IOIO72/scad-amiga-clock/20210601_144001.jpg

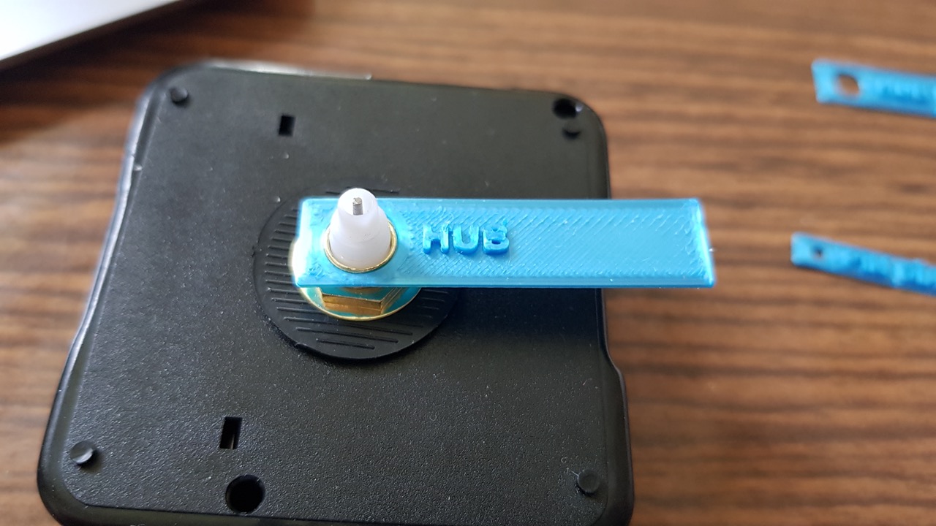
20210601_144001.jpg
