IOIO72/scad-amiga-clock/20210601_144141.jpg

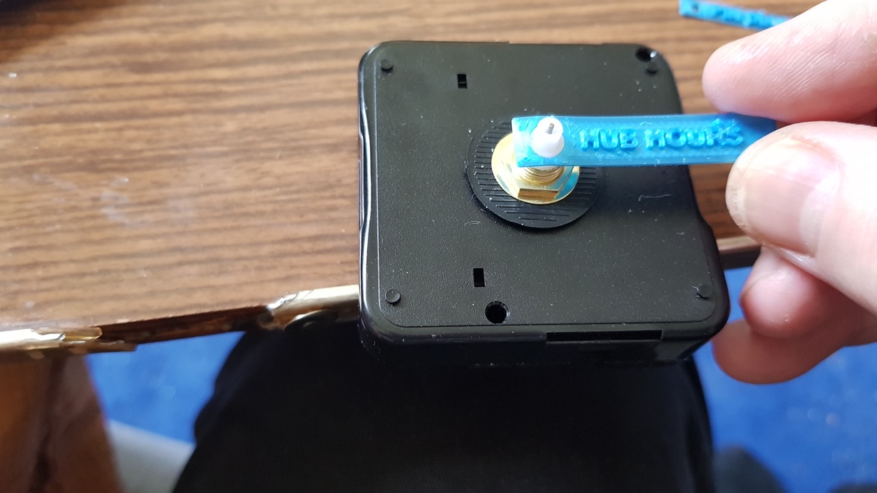
20210601_144141.jpg
