IOIO72/scad-amiga-clock/20210601_144154.jpg

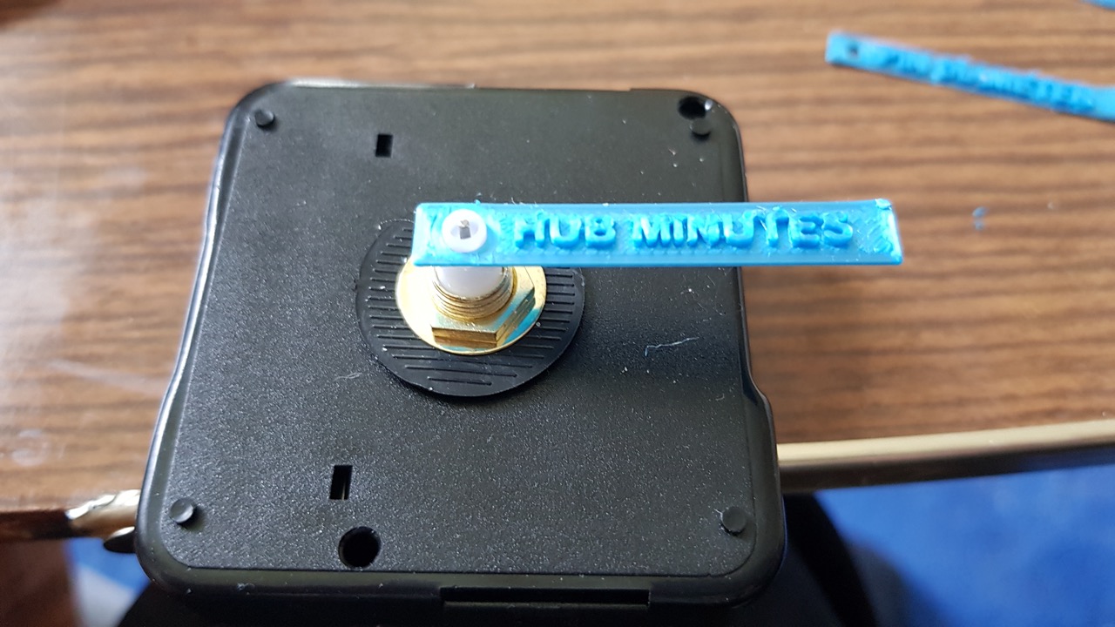
20210601_144154.jpg
