IOIO72/scad-amiga-clock/20210601_144229.jpg

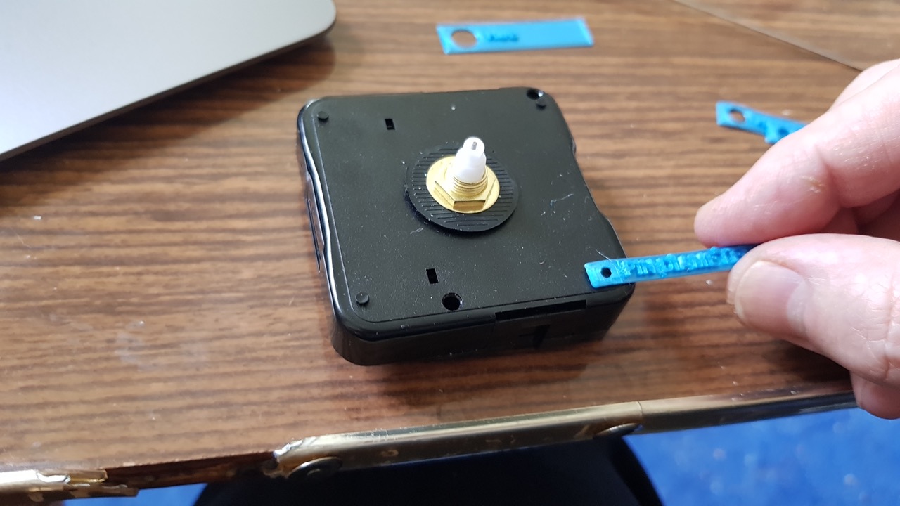
20210601_144229.jpg
