IOIO72/scad-amiga-clock/20210601_170503.jpg

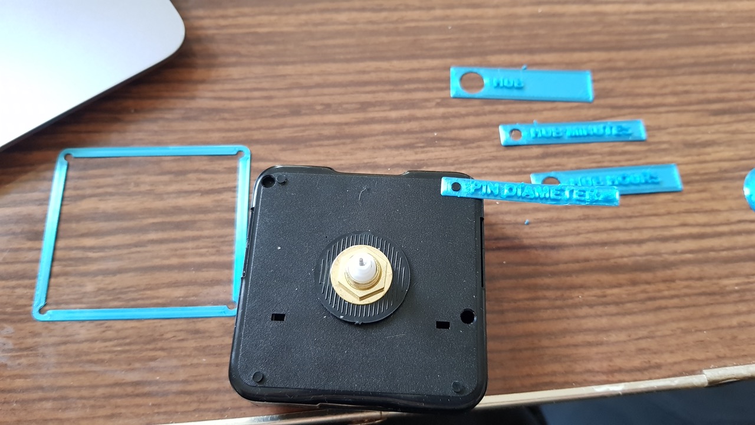
20210601_170503.jpg
