IOIO72/scad-amiga-clock/20210601_170538.jpg

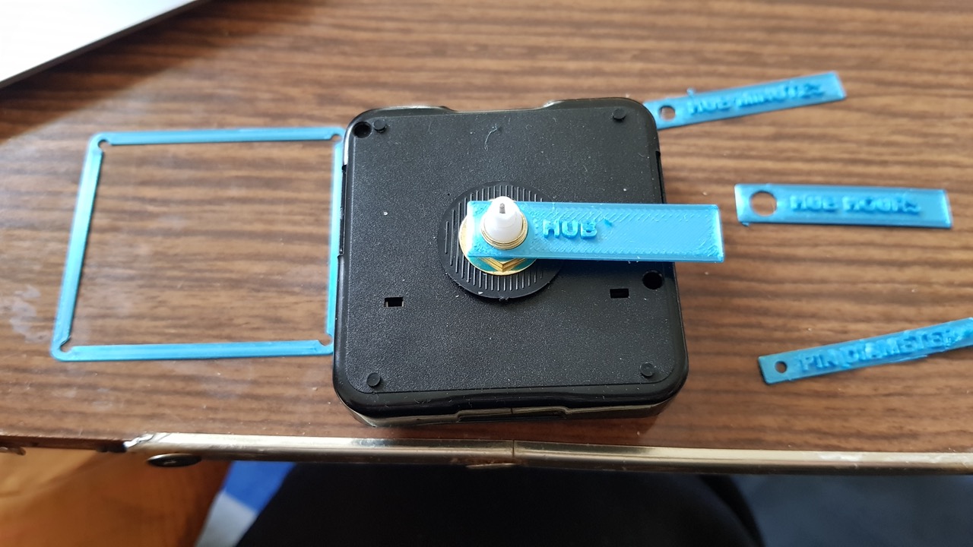
20210601_170538.jpg
