IOIO72/scad-amiga-clock/20210601_170613.jpg

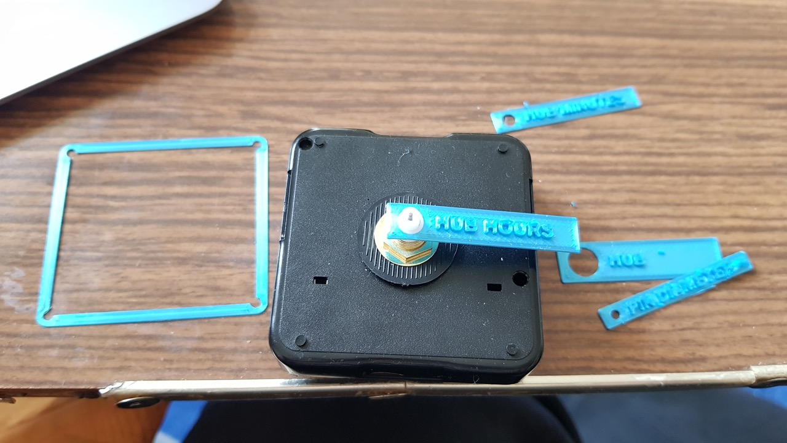
20210601_170613.jpg
