IOIO72/scad-amiga-clock/20210601_170634.jpg

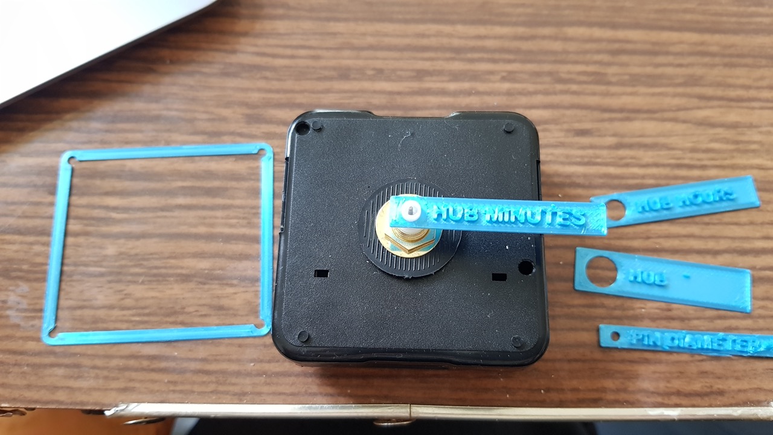
20210601_170634.jpg
