IOIO72/scad-amiga-clock/20210601_195533.jpg

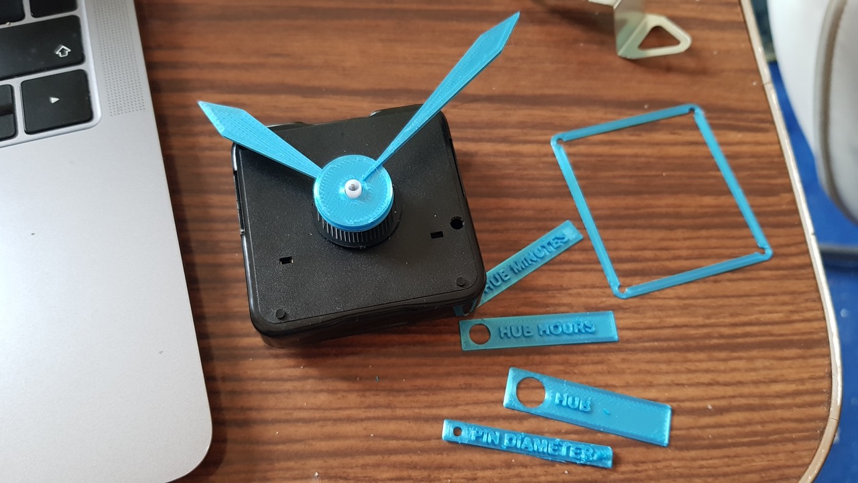
20210601_195533.jpg
