IOIO72/scad-amiga-clock/20210601_195553.jpg

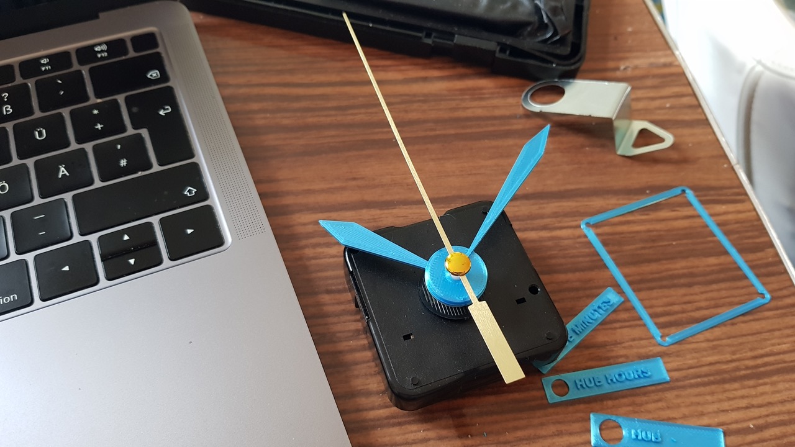
20210601_195553.jpg
