IOIO72/scad-amiga-clock/20210601_195704.jpg

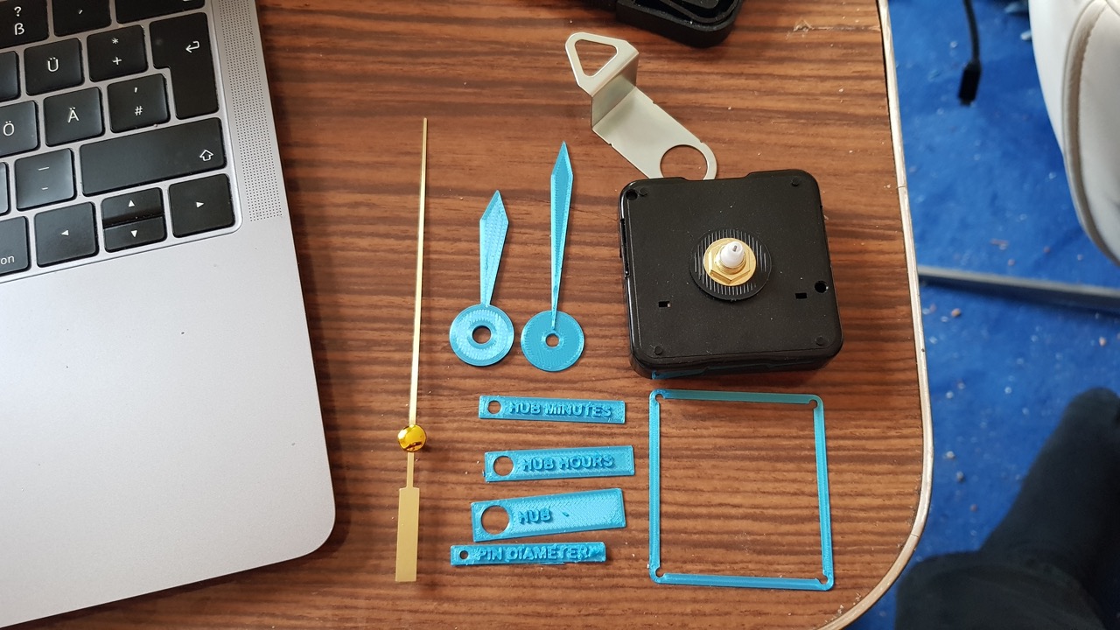
20210601_195704.jpg
