IOIO72/scad-amiga-clock/20210601_195735.jpg

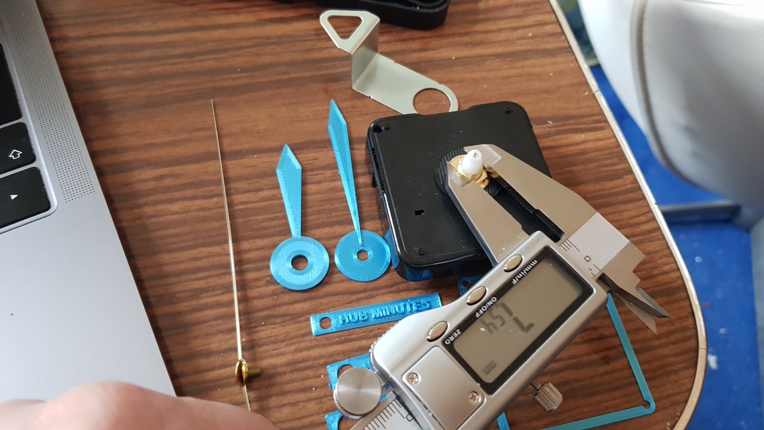
20210601_195735.jpg
