IOIO72/scad-amiga-clock/20210601_195748.jpg

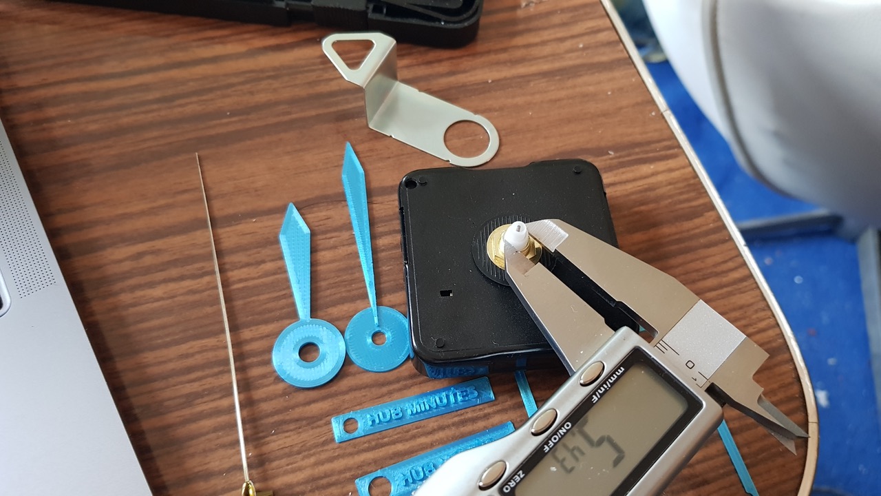
20210601_195748.jpg
