IOIO72/scad-amiga-clock/20210601_195756.jpg

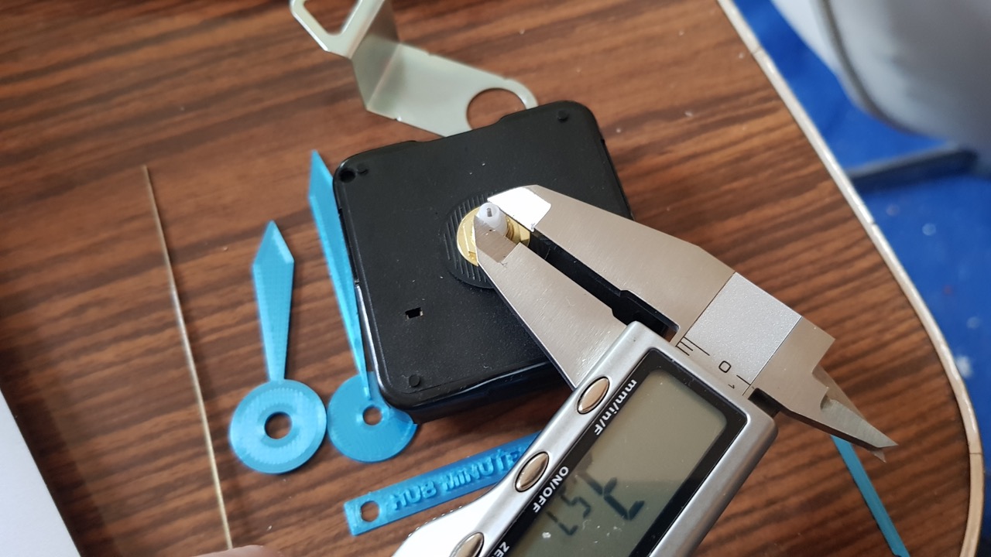
20210601_195756.jpg
