IOIO72/scad-amiga-clock/20210601_195808.jpg

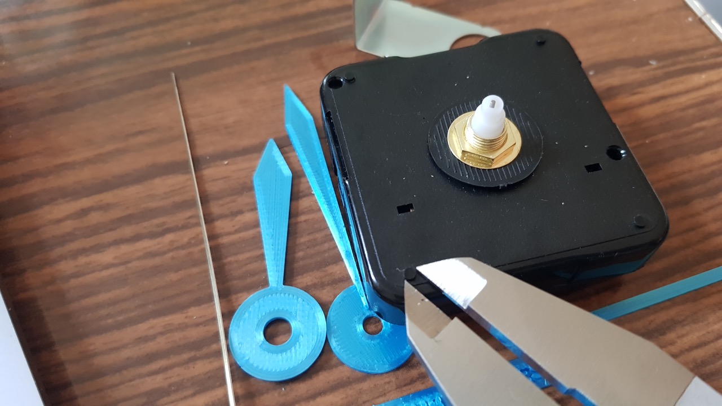
20210601_195808.jpg
