IOIO72/scad-amiga-clock/20210601_195823.jpg

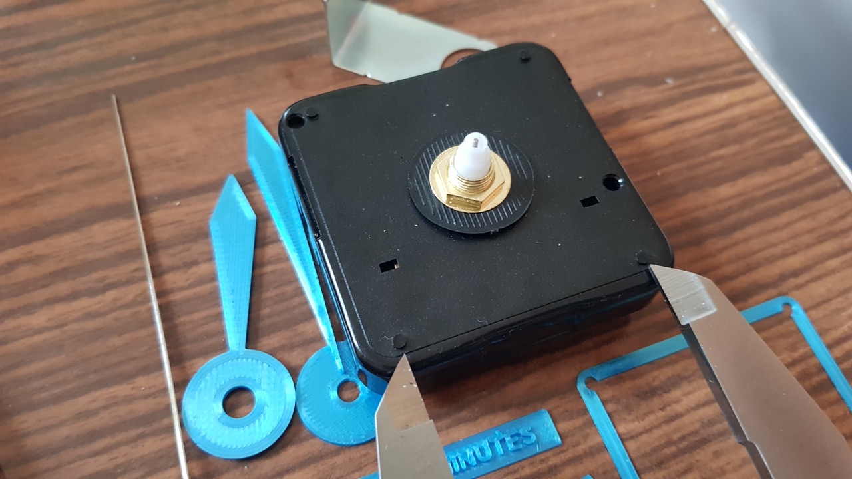
20210601_195823.jpg
