IOIO72/scad-amiga-clock/20210601_195827.jpg

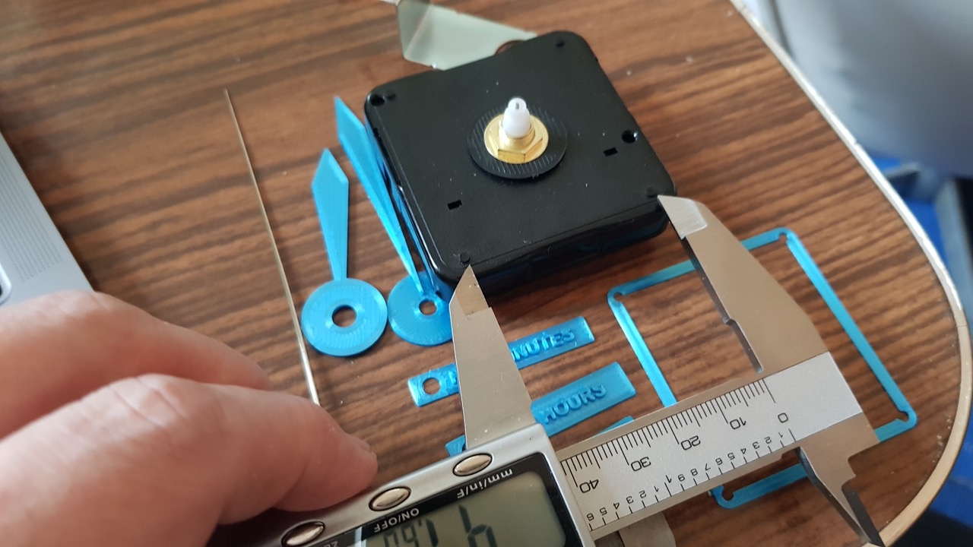
20210601_195827.jpg
