IOIO72/scad-amiga-clock/20210601_205004.jpg

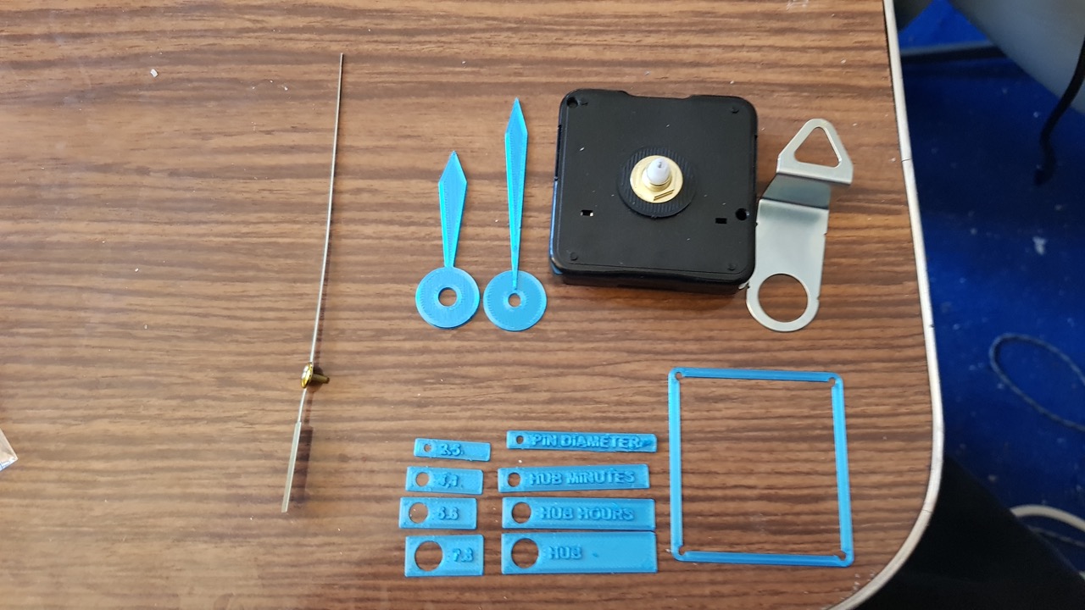
20210601_205004.jpg
