IOIO72/scad-amiga-clock/20210601_205012.jpg

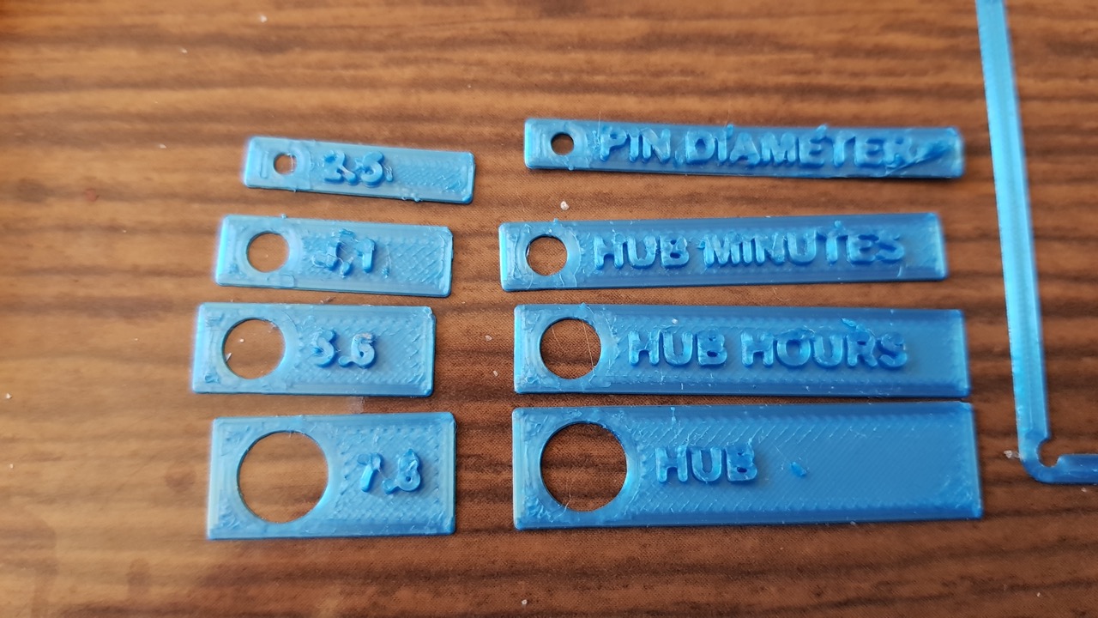
20210601_205012.jpg
