IOIO72/scad-amiga-clock/20210601_205309.jpg

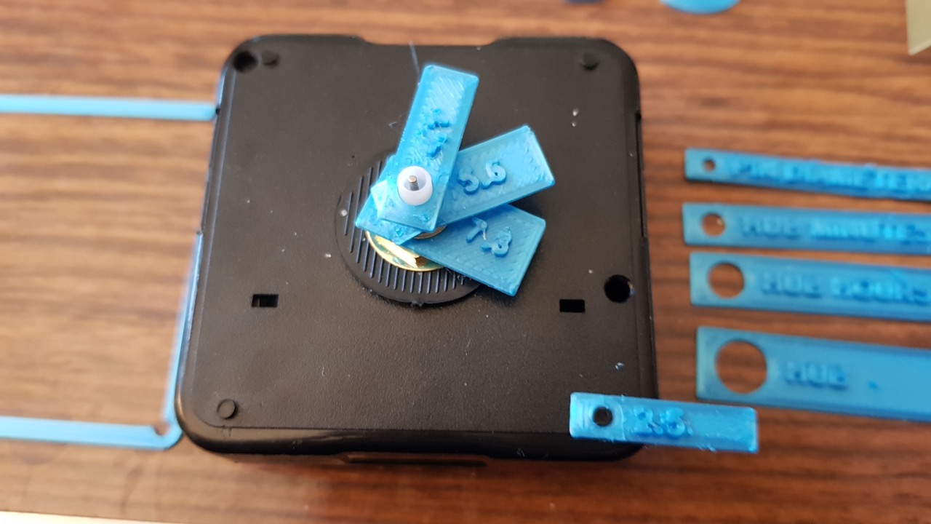
20210601_205309.jpg
