IOIO72/scad-amiga-clock/20210601_205401.jpg

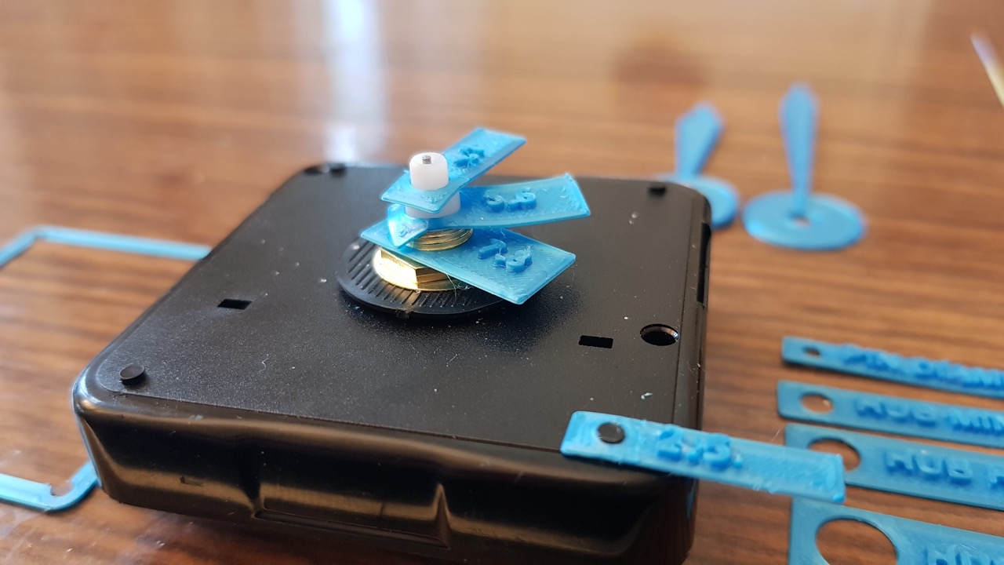
20210601_205401.jpg
