IOIO72/scad-amiga-clock/20210603_113448.jpg

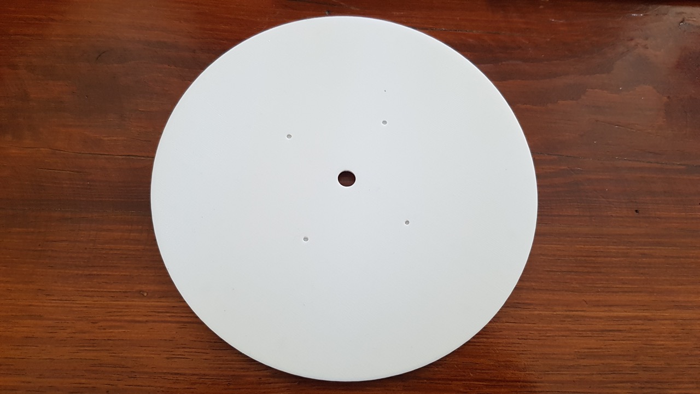
20210603_113448.jpg
