IOIO72/scad-amiga-clock/20210603_113506.jpg

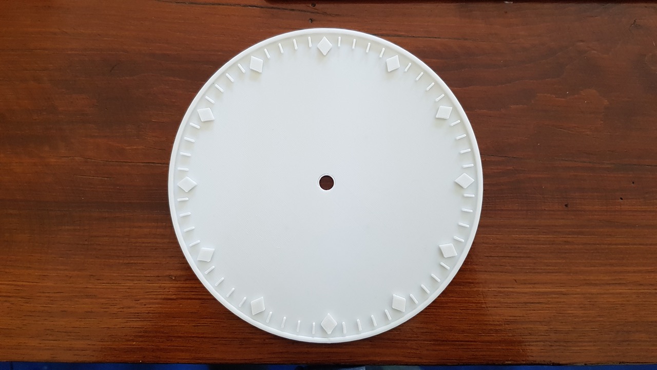
20210603_113506.jpg
