IOIO72/scad-amiga-clock/20210603_114053.jpg

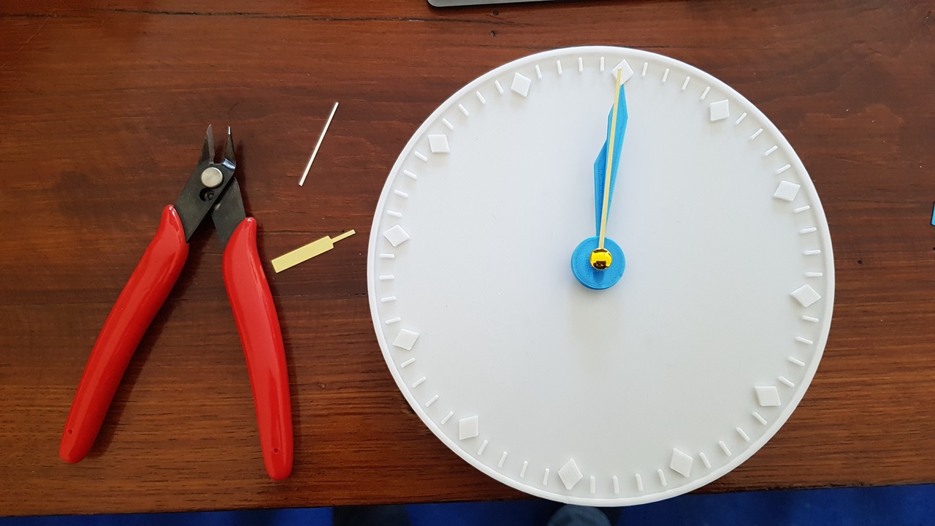
20210603_114053.jpg
