IOIO72/scad-amiga-clock/20210603_114148.jpg

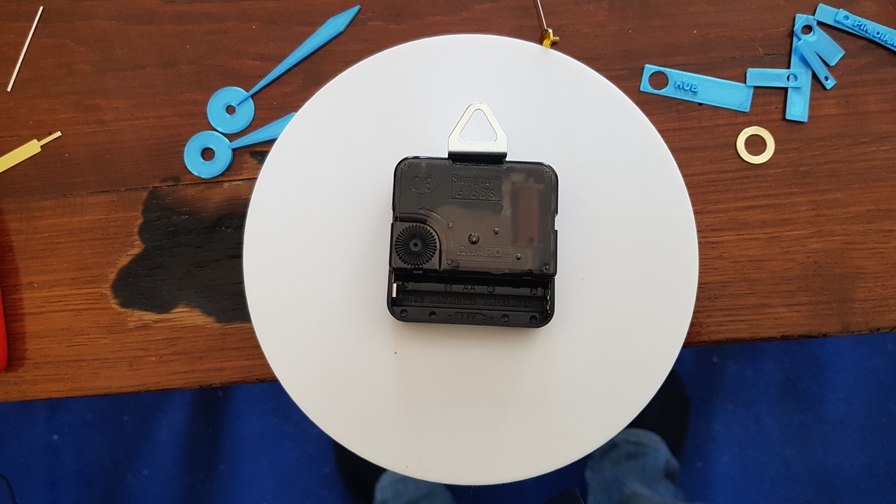
20210603_114148.jpg
