IOIO72/scad-amiga-clock/20210603_143512.jpg

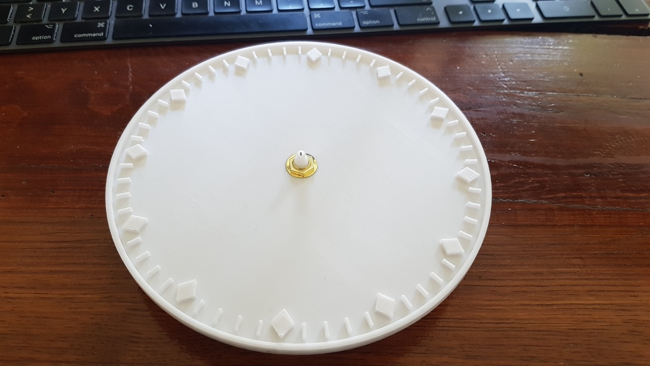
20210603_143512.jpg
