IOIO72/scad-amiga-clock/20210603_215455.jpg

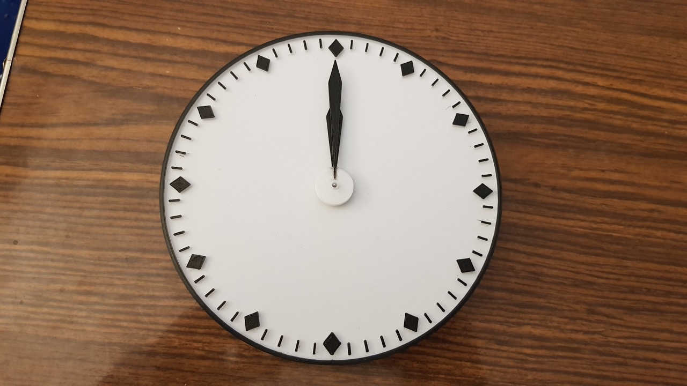
20210603_215455.jpg
