IOIO72/scad-amiga-clock/20210603_215640.jpg

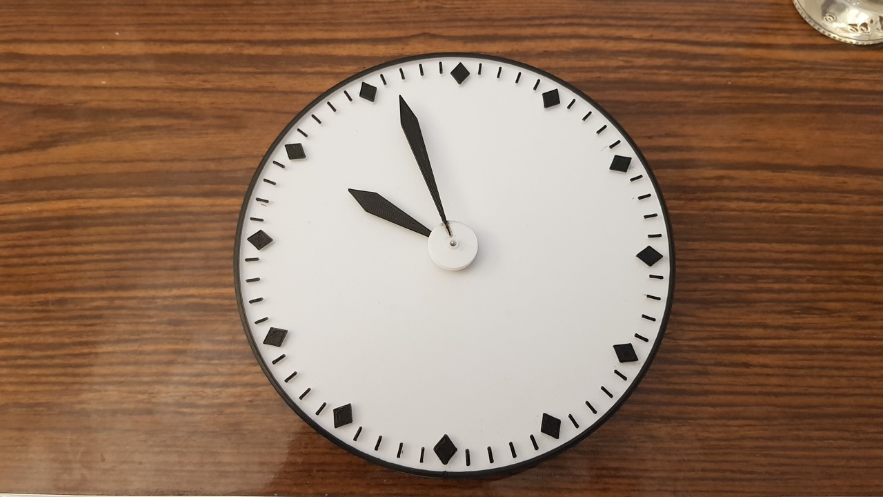
20210603_215640.jpg
