IOIO72/scad-amiga-clock/20210603_221211.jpg

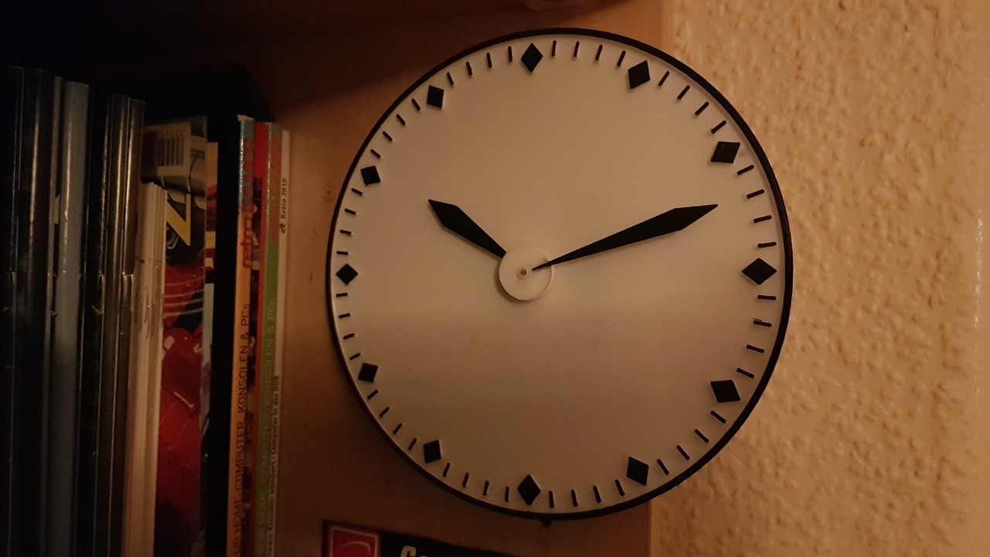
20210603_221211.jpg
