IOIO72/scad-amiga-clock/20210603_221223.jpg

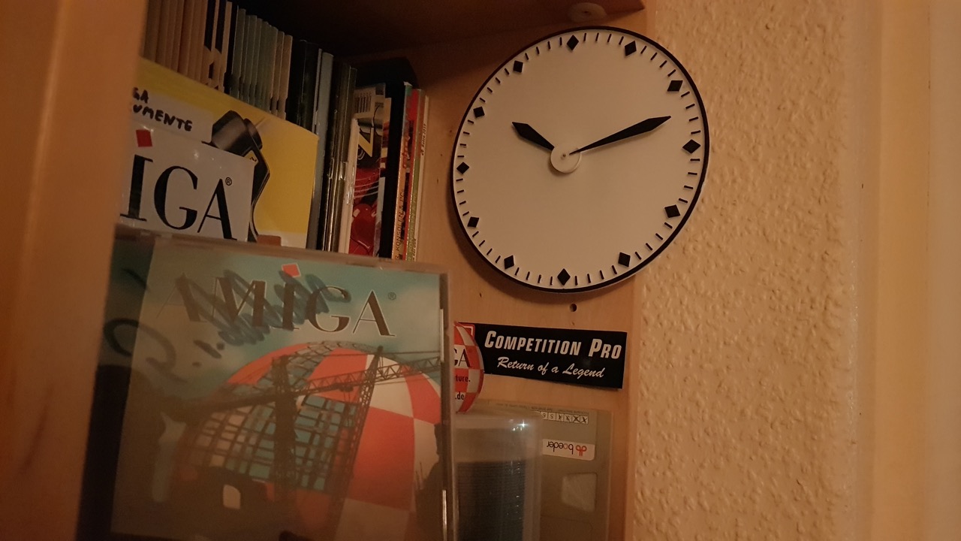
20210603_221223.jpg
