IOIO72/scad-amiga-clock/20210603_221235.jpg

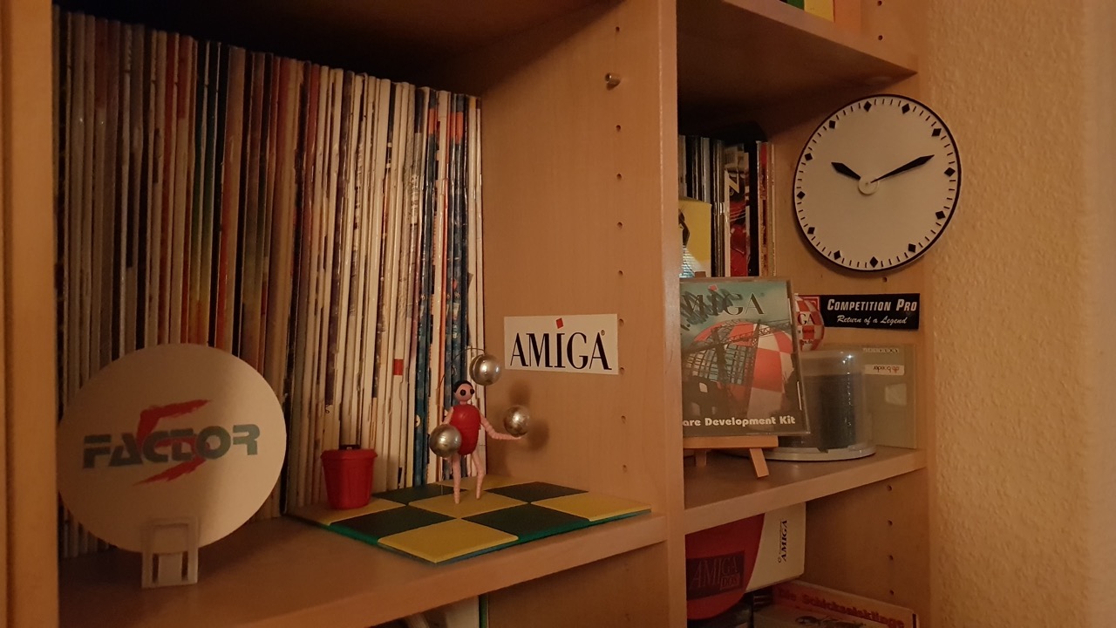
20210603_221235.jpg
