IOIO72/scad-amiga-clock/20210604_154106.jpg

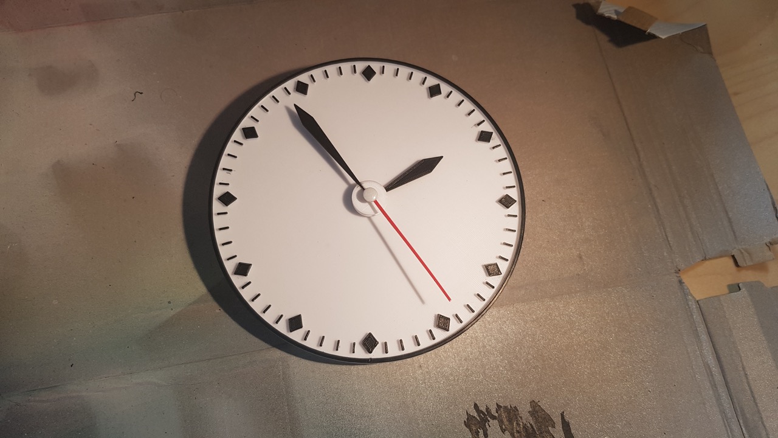
20210604_154106.jpg
