IOIO72/scad-amiga-clock/20210604_154109.jpg

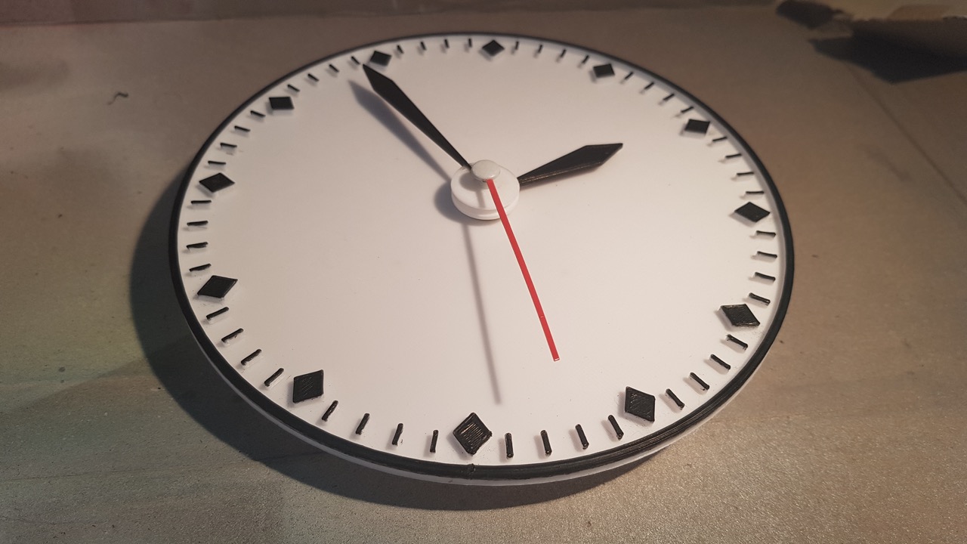
20210604_154109.jpg
