IOIO72/scad-amiga-clock/amiga-clock.gif

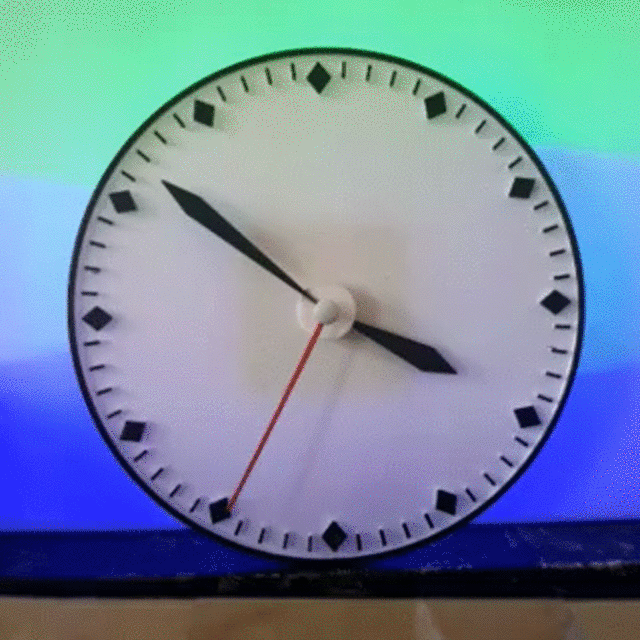
amiga-clock.gif
